conejoninja/barones-app/plugins/com.megster.cordova.bluetoothserial/examples/Chat/www/img/bg_dark.png

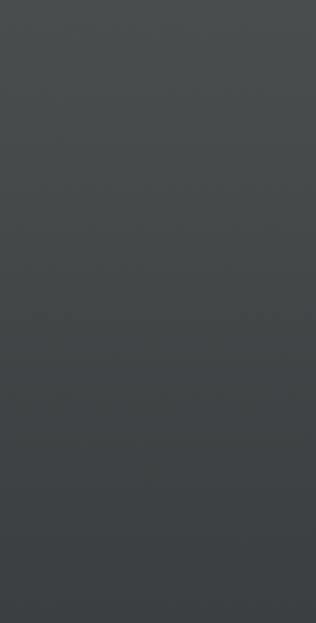
plugins/com.megster.cordova.bluetoothserial/examples/Chat/www/img/bg_dark.png
