conejoninja/barones-app/plugins/com.megster.cordova.bluetoothserial/examples/Chat/www/img/cordova.png

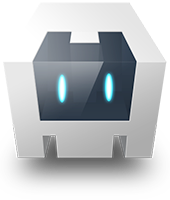
plugins/com.megster.cordova.bluetoothserial/examples/Chat/www/img/cordova.png
