conejoninja/barones-app/plugins/com.megster.cordova.bluetoothserial/examples/Chat/www/img/dialog-zone-bg.png

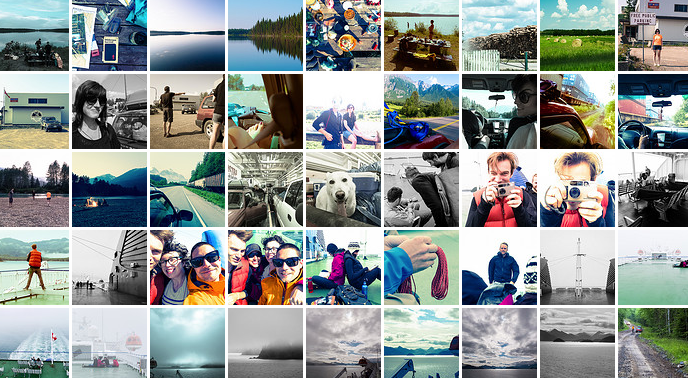
plugins/com.megster.cordova.bluetoothserial/examples/Chat/www/img/dialog-zone-bg.png
