conejoninja/barones-app/plugins/com.megster.cordova.bluetoothserial/examples/Chat/www/res/screen/android_hdpi_landscape.png

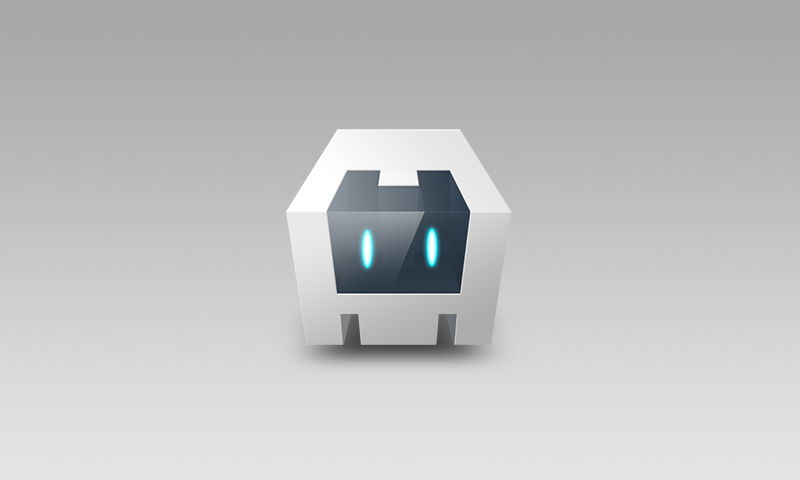
plugins/com.megster.cordova.bluetoothserial/examples/Chat/www/res/screen/android_hdpi_landscape.png
