conejoninja/barones-app/plugins/com.megster.cordova.bluetoothserial/examples/Chat/www/res/screen/android_mdpi_landscape.png

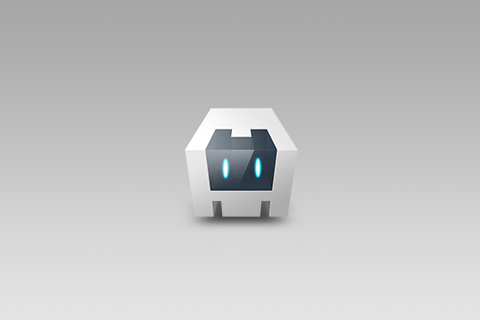
plugins/com.megster.cordova.bluetoothserial/examples/Chat/www/res/screen/android_mdpi_landscape.png
