conejoninja/barones-app/plugins/com.megster.cordova.bluetoothserial/examples/Chat/www/res/screen/blackberry_transparent_400.png

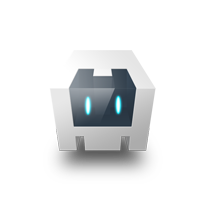
plugins/com.megster.cordova.bluetoothserial/examples/Chat/www/res/screen/blackberry_transparent_400.png
