conejoninja/barones-app/plugins/com.megster.cordova.bluetoothserial/examples/Chat/www/res/screen/ipad_retina_portrait.png

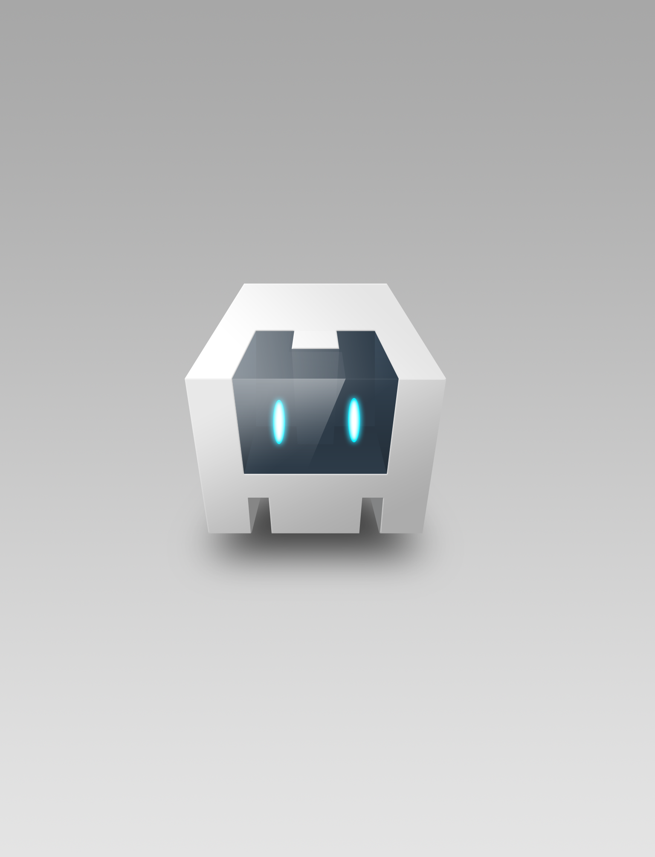
plugins/com.megster.cordova.bluetoothserial/examples/Chat/www/res/screen/ipad_retina_portrait.png
