conejoninja/barones-app/plugins/com.megster.cordova.bluetoothserial/examples/Chat/www/res/screen/iphone_portrait.png

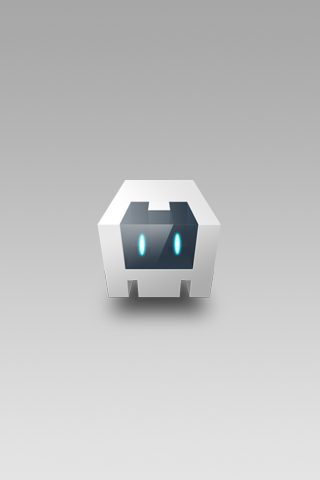
plugins/com.megster.cordova.bluetoothserial/examples/Chat/www/res/screen/iphone_portrait.png
