conejoninja/barones-app/plugins/org.apache.cordova.camera/src/ubuntu/back.png

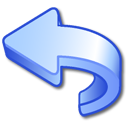
plugins/org.apache.cordova.camera/src/ubuntu/back.png
