conejoninja/barones-app/plugins/org.apache.cordova.camera/src/ubuntu/shoot.png

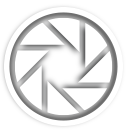
plugins/org.apache.cordova.camera/src/ubuntu/shoot.png
