conejoninja/barones-app/plugins/org.apache.cordova.camera/src/ubuntu/toolbar-left.png

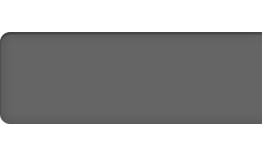
plugins/org.apache.cordova.camera/src/ubuntu/toolbar-left.png
