conejoninja/barones-app/plugins/org.apache.cordova.camera/src/ubuntu/toolbar-middle.png

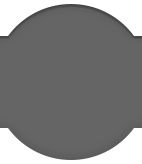
plugins/org.apache.cordova.camera/src/ubuntu/toolbar-middle.png
