conejoninja/barones-app/www/img/connecting.gif

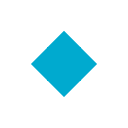
www/img/connecting.gif
