conejoninja/barones-app/www/res/screen/android/screen-hdpi-landscape.png

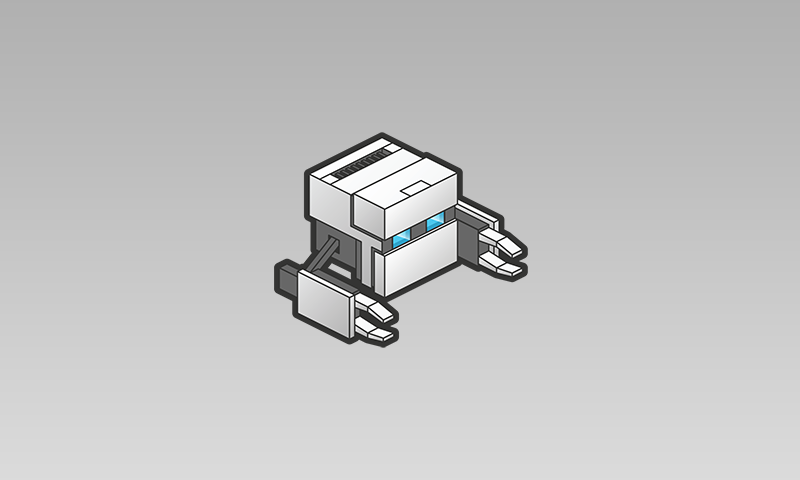
www/res/screen/android/screen-hdpi-landscape.png
