conejoninja/barones-app/www/res/screen/android/screen-hdpi-portrait.png

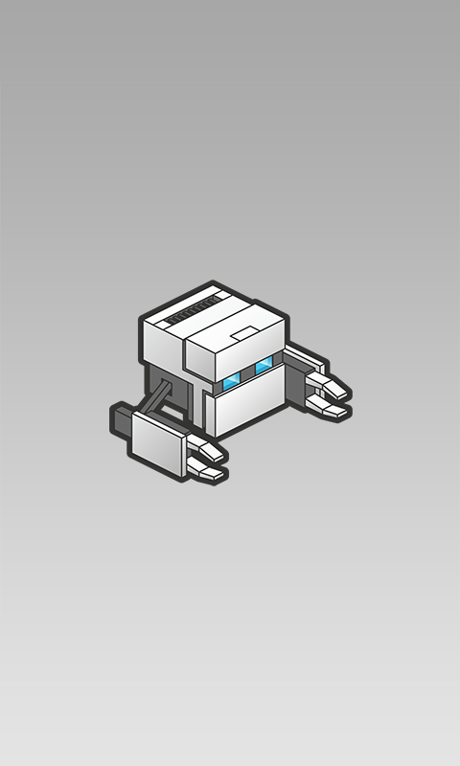
www/res/screen/android/screen-hdpi-portrait.png
