conejoninja/barones-app/www/res/screen/blackberry/screen-225.png

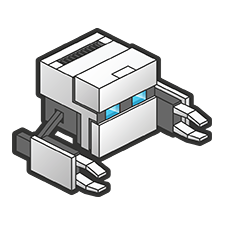
www/res/screen/blackberry/screen-225.png
