conejoninja/barones-app/www/res/screen/ios/screen-ipad-portrait-2x.png

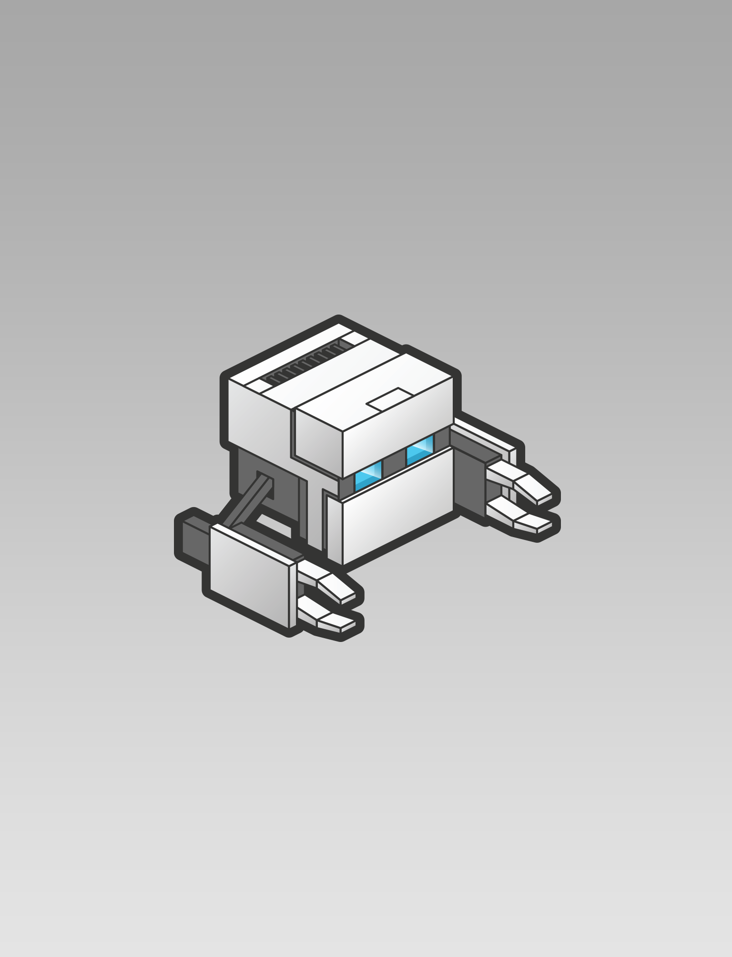
www/res/screen/ios/screen-ipad-portrait-2x.png
